MarianAldenhoevel/DoorSign/Firmware/core1.py

'''
This module implements the animation task.

It loads all modules named animation_*.py found in the current folder and checks their enabled-value. If
enabled the animation is added to a pool of available animations.

If there aren't any enabled animations the task ends. Otherwise one is selected at random as the active
animation.

If there are two or more animations enabled the task will after a while select a next animation from
the pool and blend between the two.

Care is taken that all enabled animations are used and never back-to-back.
'''

preferred_animation_blend_ms = 60 * 1000 # Blend time between animations. It may turn out shorter if an animation requests to be runs for a short time. 

# Set to empty string to request a random animation to start at the next
# possible moment or set to the name of an animation to run next.
request_animation = None 

final_dimmer = 1.0

import machine
import time
import logger
import doorsign
import random
import os
import watchdog

animations = []
active_animation = None

'''
Set up the animations by dynamically loading modules according to a naming convention
'''
def setup():
    global animations
    
    # Import all modules named animation_*.py:
    # List files, filter by name, strip off the .py extension, load as module and finally filter by their enabled variable.
    logger.write('Loading animation modules')
    animationfiles = filter(lambda file: file.startswith('animation_') and file.endswith('.py'), os.listdir())        
    modulenames = list(map(lambda file: file.split('.')[0], animationfiles))
    animations = list(map(__import__, modulenames))        
    animations = list(filter(lambda animation: animation.enabled, animations))
    
    if len(animations) == 0:
        logger.write('No animations available')
        return
    elif len(animations) > 1:
        logger.write('Available animations: ' + ', '.join(animation.__name__ for animation in animations))
    
def task():
    global active_animation
    global request_animation
     
    logger.register_thread_name('ANIM')
    watchdog.feed() # First feed to make us known to the WDT
    logger.write('Animation task starting')
    
    # Initialize two arrays. new_animations holds the animation modules that can be picked, the other
    # holds the ones that have already been run to implement draw without put back.
    new_animations = animations[:]
    old_animations = []

    active_animation = None
    next_animation = None

    # Randomly pick the first animation to execute. We are guaranteed to have one 
    # because we returned if we didn't.
    if len(animations) > 0:
        doorsign.beginUpdate()
        try:
            active_animation = random.choice(new_animations)
        finally:
            doorsign.endUpdate()
            
        new_animations.remove(active_animation)
        old_animations.append(active_animation)
        if len(new_animations) == 0:
            new_animations = old_animations
            old_animations = []
        active_animation_start_ms = time.ticks_ms()
        
        logger.write(('First' if len(animations) > 1 else 'Active') + ' animation: ' + active_animation.__name__)
    else:
        logger.write('No animation module enabled')
        
    next_animation = None

    '''
    Main animation loop
    '''
    while True:
        watchdog.feed()

        frame_ms = time.ticks_ms()
        
        if (active_animation):
            
            # Is there a requested for an animation switch? If so execute it immediately. 
            if request_animation != None:
                candidate_animation = None
                
                if (request_animation == ''):
                    if (len(animations) >= 2):
                        # Pick a random next animation to execute. Brutally sample until we do not 
                        # get the same as the active one.           
                        while True:
                            candidate_animation = random.choice(new_animations)                                                
                            if next_animation is not active_animation:
                                break
                    else:
                        logger.write('Only one single animation enabled, cannot pick next at random')
                else:
                    # Pick the next animation by name.
                    for animation in animations:
                        if animation.__name__.upper() == request_animation.upper():
                            candidate_animation = animation
                            break
                    if not candidate_animation:
                        logger.write('Next animation \"' + request_animation + '\" not found')
                
                # If we picked or found the new animation now update the lists and start
                # it immediately without a blend.
                if candidate_animation:
                    doorsign.beginUpdate()
                    try:
                        active_animation = candidate_animation
                    finally:
                        doorsign.endUpdate()
                        
                    active_animation_start_ms = frame_ms
                    next_animation = None
                    
                    if active_animation in new_animations:
                        new_animations.remove(active_animation)
                        old_animations.append(active_animation)    
                        if len(new_animations) == 0:
                            new_animations = old_animations
                            old_animations = []
                    doorsign.setManualControl(False)
            
                    logger.write('Switching to ' + ('random ' if not request_animation else '') + 'requested ' + active_animation.__name__)
                else:
                    logger.write('Could not honour request for ' + ('random ' if request_animation == '' else '') + 'next animation ' + request_animation)
                    
                # Reset request for next animation.
                request_animation = None                    
            
            # Get the pixels for the active animation.
            active_pixels = active_animation.update(frame_ms)
    
            # Are we running a next animation?
            if (next_animation):
                # Yes. Get their pixels.
                next_pixels = next_animation.update(frame_ms)
            
                # Blend between the two animations in interval milliseconds
                diff = time.ticks_diff(frame_ms, next_animation_start_ms)

                # How long should the blend be?  
                blend = diff/animation_blend_ms
                        
                if (blend >= 1.0):
                    # Finished blend. Swap animations, we will only be running the next
                    # animation as active now.
                    doorsign.beginUpdate()
                    try:
                        active_animation = next_animation
                    finally:
                        doorsign.endUpdate()
                        
                    active_animation_start_ms = frame_ms
                    next_animation = None

                    # Use the pixels of the next animation directly.
                    pixels = next_pixels
                else:
                    # Blend between the two animations' pixel arrays.
                    pixels = doorsign.blendPixels(active_pixels, next_pixels, blend)
            else:
                # No next animation scheduled at the moment. The pixels for the active animation
                # get used directly.
                pixels = active_pixels
                
                # Do we have a next animation in our portfolio and do we want it now?
                if (len(animations) >= 2) and (not doorsign.manual_control) and (time.ticks_diff(frame_ms, active_animation_start_ms) >= active_animation.preferred_duration_ms):
                    # Pick a next animation to execute. Brutally sample until we do not 
                    # get the same as the active one.           
                    while True:
                        next_animation = random.choice(new_animations)                                                
                        if next_animation is not active_animation:
                            break

                    new_animations.remove(next_animation)
                    old_animations.append(next_animation)    
                    if len(new_animations) == 0:
                        new_animations = old_animations
                        old_animations = []
                    next_animation_start_ms = frame_ms

                    logger.write('Next animation: ' + next_animation.__name__)

                    # Calculate how long to blend between active and next animation. Typically this will be the preferred
                    # value. But if the runtimes of the active or next animations are short trim it.
                    animation_blend_ms = min(preferred_animation_blend_ms, active_animation.preferred_duration_ms // 2, next_animation.preferred_duration_ms // 2) 
            
        else:
            # No animation at all. All off.
            pixels = [[0, 0, 0]] * doorsign.pixel_count
        
        pixels = doorsign.scalePixels(pixels, final_dimmer);
        
        # Output the pixels only if currently not under manual control. Animation
        # keeps running.
        if not doorsign.manual_control:
            doorsign.setPixels(pixels)
        
        # Sleep for the remainder of the frame if any.
        now_ms = time.ticks_ms()
        used_ms = time.ticks_diff(now_ms, frame_ms)
        remaining_ms = doorsign.frame_intervall_ms - used_ms
   
        if remaining_ms > 0:
            time.sleep_ms(remaining_ms)
   
if __name__ == '__main__':
    
    logger.write('Running stand-alone task()')
    setup()
    task()
    logger.write('task() exited')
